LED-BOY/wrist-watch/Game_Light_watch_2_2.2/digits.h

/*
    This file is part of Game&Light Timer

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
    To contact us: ledboy.net
    ledboyconsole@gmail.com
*/
//  numbers
const uint8_t number0 [] = {
  0x00, 0xfc, 0xfe, 0xff, 0x0f, 0x07, 0x07, 0x07, 0x07, 0x07, 0x07, 0x07, 0x07, 0x07, 0x07,
  0x07, 0x07, 0x07, 0x07, 0x07, 0x07, 0x07, 0x07, 0x07, 0x07, 0x07, 0x07, 0x0f, 0xff, 0xfe,
  0xfc, 0x00, 0x00, 0x3f, 0x7f, 0xff, 0xf0, 0xe0, 0xe0, 0xe0, 0xe0, 0xe0, 0xe0, 0xe0, 0xe0, 0xe0, 0xe0,
  0xe0, 0xe0, 0xe0, 0xe0, 0xe0, 0xe0, 0xe0, 0xe0, 0xe0, 0xe0, 0xe0, 0xe0, 0xf0, 0xff, 0x7f,
  0x3f, 0x00
};

const uint8_t number1[] = {
  0x00, 0x00, 0x00, 0x00, 0x00, 0x00, 0x00, 0x00, 0x00, 0x00, 0x00, 0x00, 0x00, 0x00, 0x00,
  0x00, 0x00, 0x00, 0x00, 0x00, 0x00, 0x00, 0x00, 0x00, 0x00, 0x00, 0x00, 0x00, 0x00, 0x00,
  0x00, 0x00,  0x00, 0x20, 0x60, 0xe0, 0xe0, 0xe0, 0xe0, 0xe0, 0xe0, 0xe0, 0xe0, 0xe0, 0xe0, 0xe0, 0xe0,
  0xe0, 0xe0, 0xe0, 0xe0, 0xe0, 0xe0, 0xe0, 0xe0, 0xe0, 0xe0, 0xe0, 0xe0, 0xe0, 0xe0, 0x60,
  0x20, 0x00
};


const uint8_t number2[] = {
  0x00, 0xfc, 0xfe, 0xff, 0x0f, 0x07, 0x07, 0x07, 0x07, 0x07, 0x07, 0x07, 0x07, 0x07, 0x0f,
  0xff, 0xfe, 0xfc, 0x00, 0x00, 0x00, 0x00, 0x00, 0x00, 0x00, 0x00, 0x00, 0x00, 0xff, 0xfe,
  0xfc, 0x00, 0x00, 0x3f, 0x7f, 0xff, 0x00, 0x00, 0x00, 0x00, 0x00, 0x00, 0x00, 0x00, 0x00, 0x00, 0x00,
  0x3f, 0x7f, 0xff, 0xf0, 0xe0, 0xe0, 0xe0, 0xe0, 0xe0, 0xe0, 0xe0, 0xe0, 0xf0, 0xff, 0x7f,
  0x3f, 0x00
};

const uint8_t number3[] = {
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
  0xff, 0xff, 0xf0, 0xe0, 0xe0, 0xe0, 0xe0, 0xe0, 0xe0, 0xe0, 0xe0, 0xe0, 0xf0, 0xff, 0x7f,
  0x3f, 0x00
};

// Array containing all numbers array
const uint16_t numbers[] = {
  number0, number1, number2, number3, number4, number5, number6, number7, number8, number9
};
